thenniges/blacktop/doc/TPS/TPS Report 4_6_20.pdf

CS 4910
Project: Blacktop
TPS Report
4/6/2020
Team: | Skyler Sheler | skyler.j.sheler@wmich.edu | (616) 438-3527
| Erron Johnson | erron.d.johnson@wmich.edu | (269) 547-8933
| Allin Kahrl | f.allin.kahrl@wmich.edu | (207) 522-4859
| Tyler Henniges | tyler.m.henniges@wmich.edu | (269) 330-4229
Client: | WMU Computer Club colin.c.maccreery@wmich.edu | (269) 276-3106
Contact: | Colin MacCreery | colin.c.maccreery@wmich.edu | (269) 276-3106
Project Lead Allin Kahrl | f.allin.kahrl@wmich.edu | (207) 522-4859
Task | Who will complete | Time | Risk 1-10 | % complete | Actual time | review
T1 | SS | 1 hour | 1 | 100% | 1 hour | AK TH EJ
T2 | TH | 5 hours | 3 | 100% | 5 hours | SS AK EJ
T3 | AK | 3 weeks | 5 | 25% | TBD | TBD
T4 | EJ | 3 weeks | 3 | 33% | TBD | TBD
T5 | EJ | 1 week | 1 | 75% | TBD | TBD
T6 | SS AK EJ TH | 3 weeks | 1 | 15% | TBD | TBD
T7 | SS AK EJ TH | 3 weeks | 1 | 15% | TBD | TBD

T1: Write the requested deliverables for the week
Write the TPS Report and Stories for the week
T2: Resolve errors with the EEPROM SPI Driver
T3: Assemble and manufacture the preliminary test jig
T4: Create use cases for the board from previous CS2230 projects T5: Revise the powerpoint slides for our final presentation
T6: Write the testing report
T7: Write the maintenance report
