thenniges/blacktop/hw/v02/blacktop_schematic.pdf

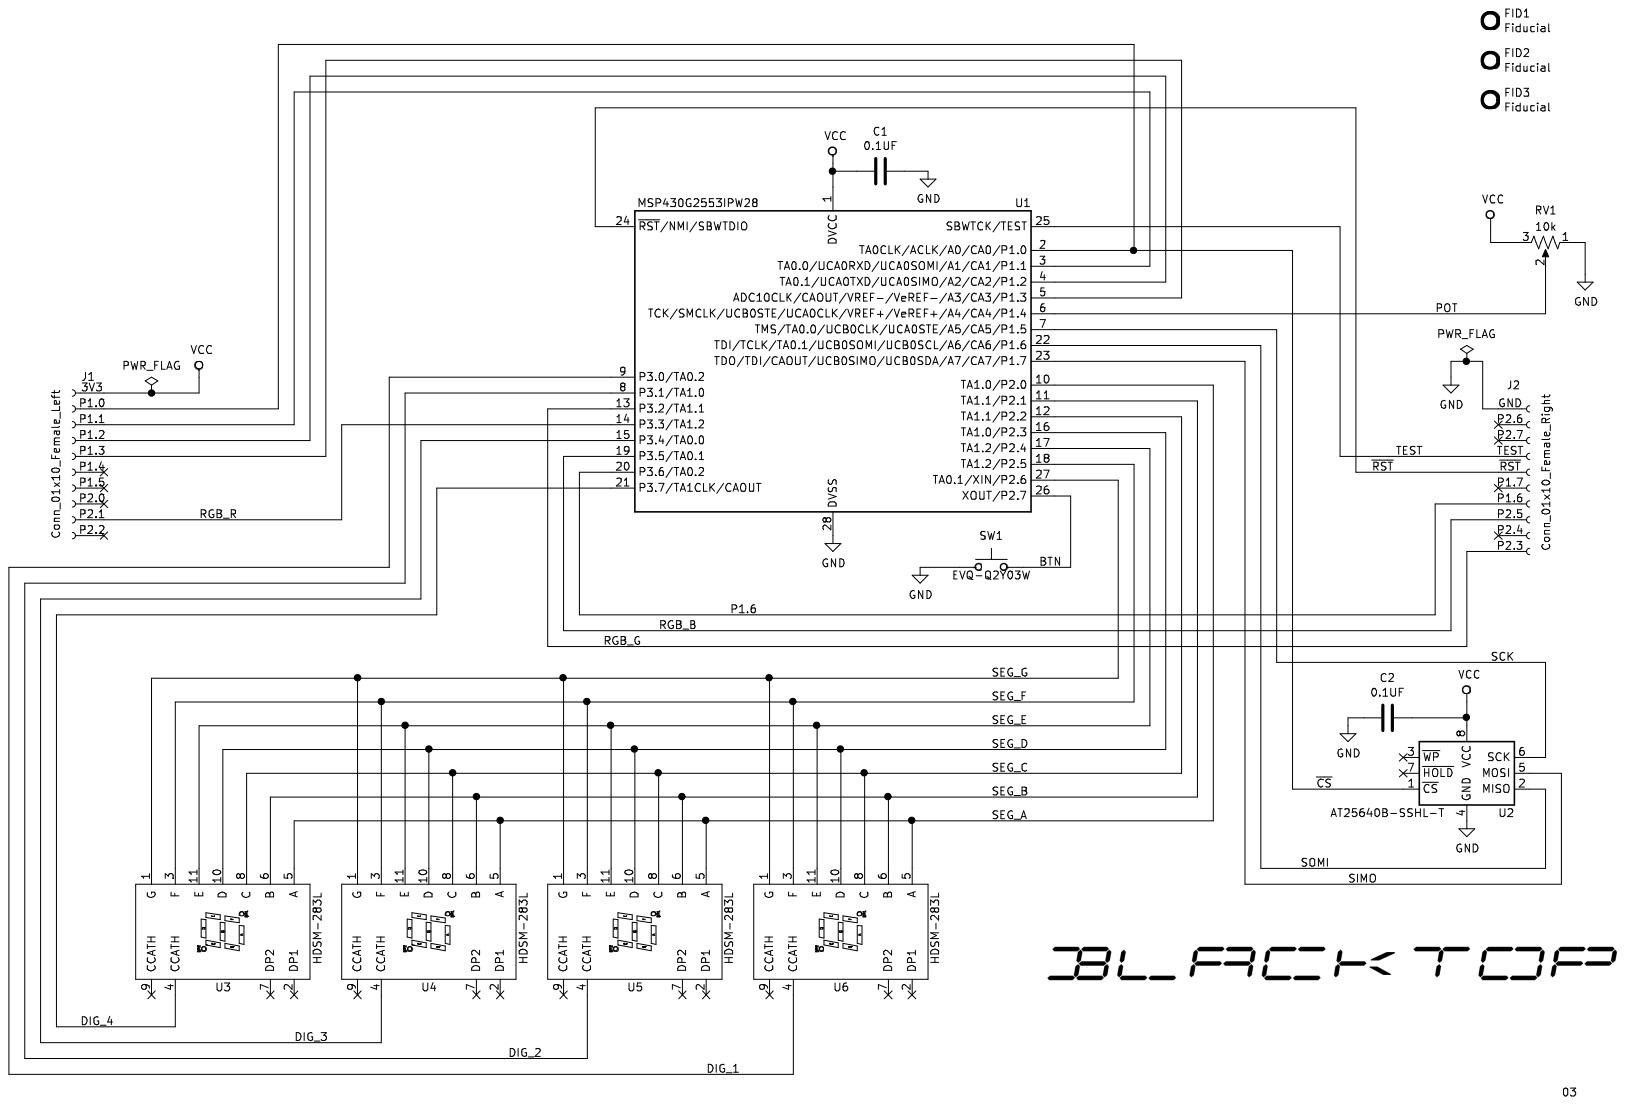
[picture p18: page 1]
